AnMayVaa/NFC-bracelet/hardware/3d/drawings/sheet2-checkin-station.png

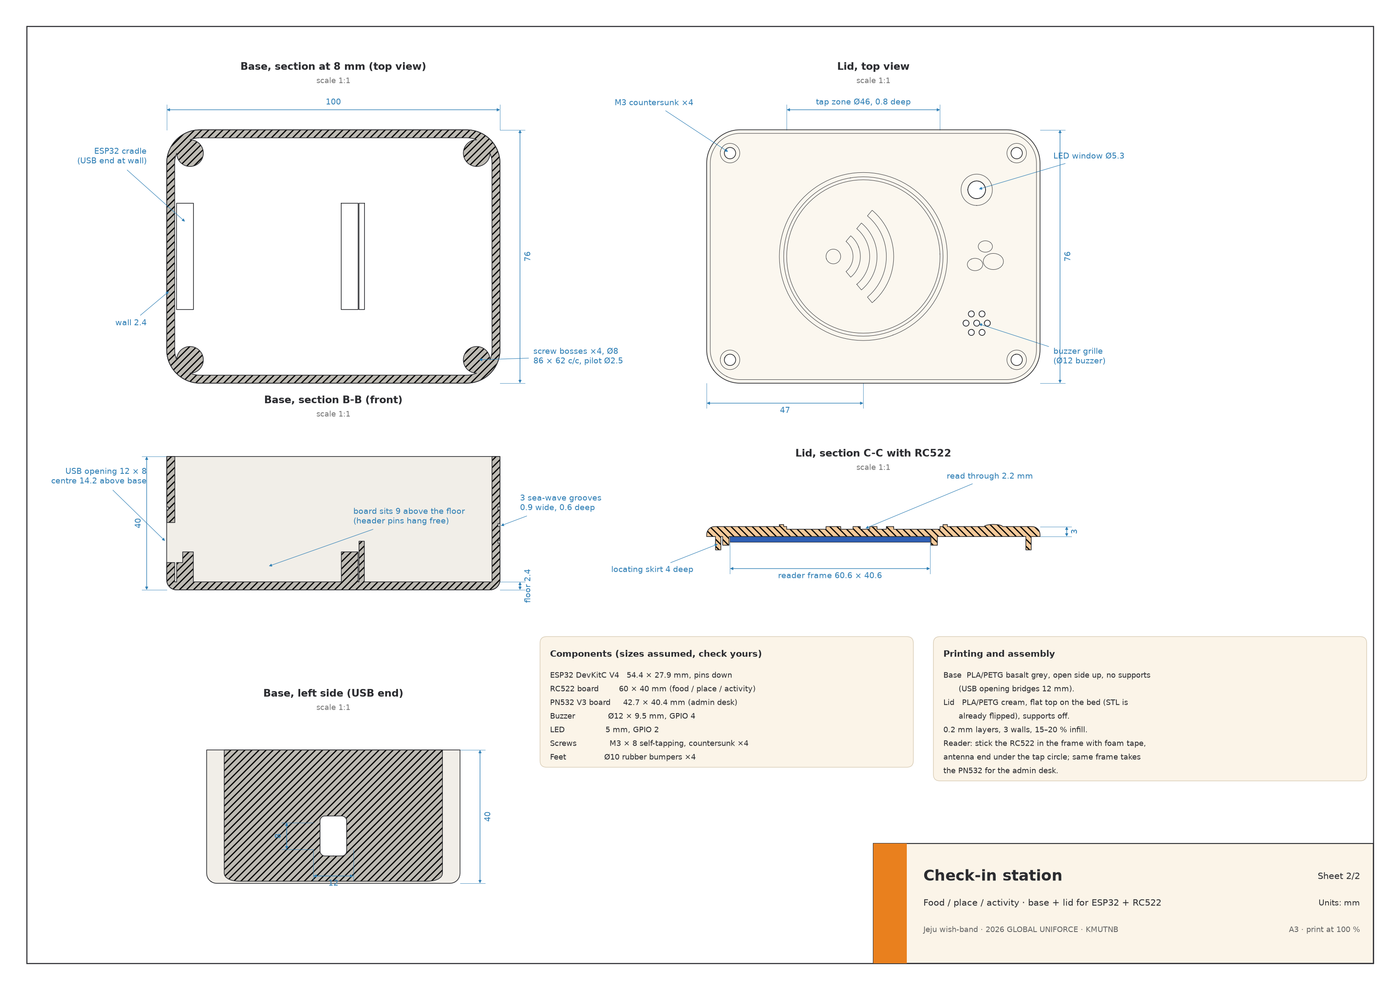
hardware/3d/drawings/sheet2-checkin-station.png
